emeb/r820t2/f030_r820t2/led.h

/*
 * led.c - f030 breakout LED setup
 */

#ifndef __led__
#define __led__

#include "stm32f0xx.h"

#define LED1 (1 << 1) /* port B bit 1 */

void led_init(void);
void led_on(uint32_t LED);
void led_off(uint32_t LED);
void led_toggle(uint32_t LED);

#endif
