emeb/r820t2/f030_r820t2/systick.h

/*
 * systick.h - systick routines
 */

#ifndef __systick__
#define __systick__

#include "stm32f0xx.h"

void systick_init(void);
void systick_delayms(uint32_t ms);
uint32_t systick_gettick(void);

#endif
